JMUWRobotics/sensorcube/examples/python/printSerialData.py

import os
import serial 
import json

# load config file (same directory as this file)
configFile = open(os.path.dirname(os.path.abspath(__file__)) + '/../../config.json')
config = json.load(configFile)

print("Opening port " + str(config["serial_port"]) + " with baudrate " + str(config["serial_baudrate"]) + ".")

# open serial port
sensorcube = serial.Serial(port=config["serial_port"], baudrate=config["serial_baudrate"])

while True:
    try:
        print(sensorcube.readline().decode('utf-8').rstrip())
    except KeyboardInterrupt:
        break
